yawkat/GridFlock/docs/images/edge-puzzle-clickgroove.png

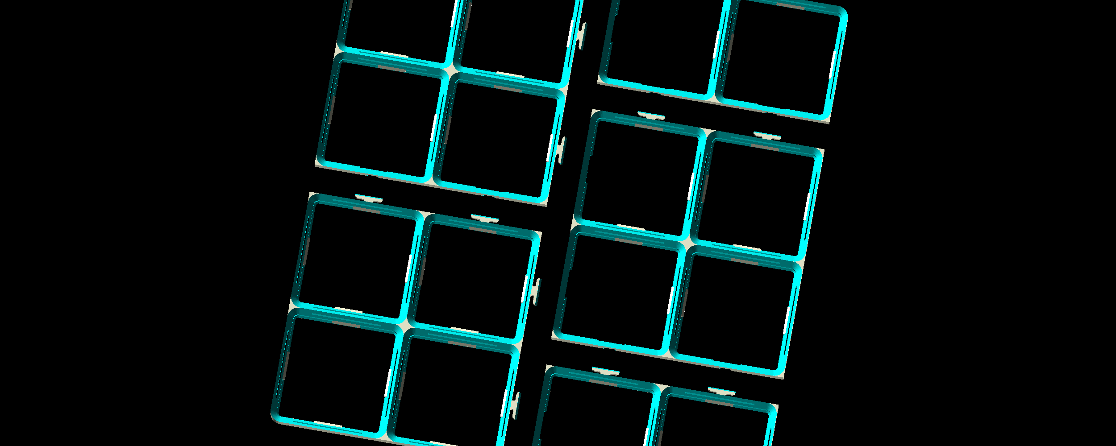
docs/images/edge-puzzle-clickgroove.png
