yawkat/GridFlock/docs/screenshot-generator-perplexinglabs.png

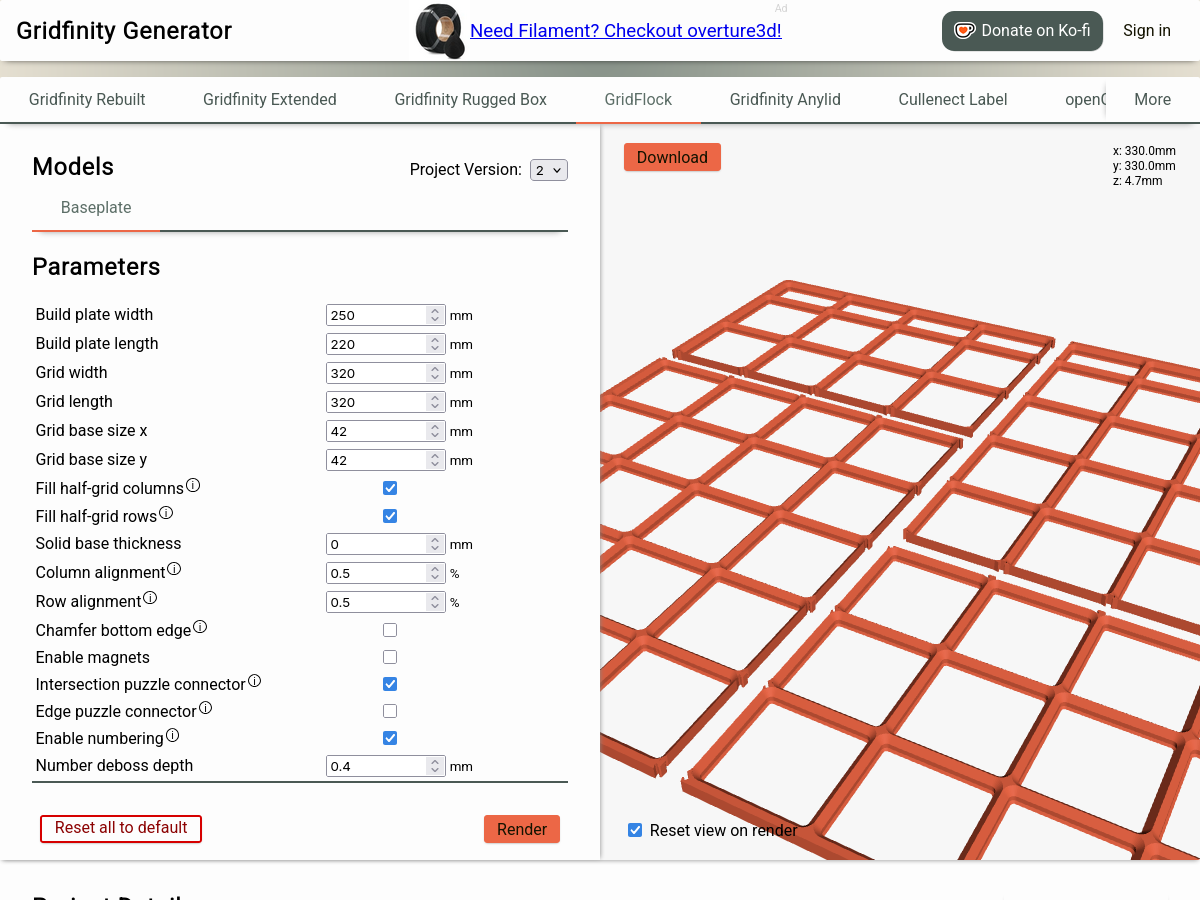
docs/screenshot-generator-perplexinglabs.png
