yawkat/GridFlock/docs/screenshot-generator-yawkat.png

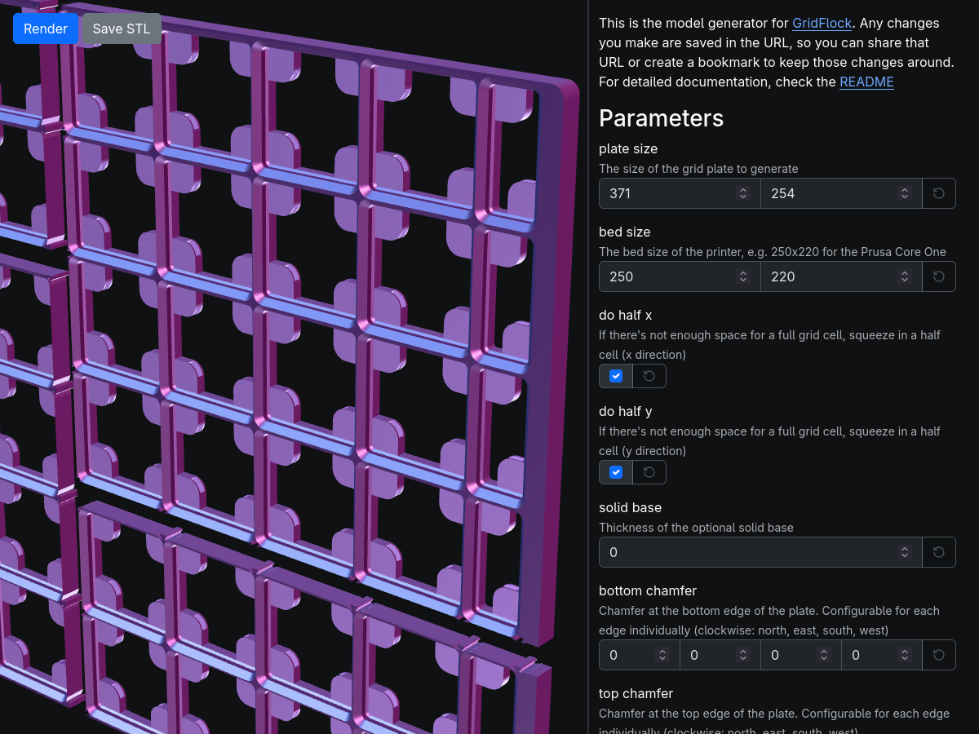
docs/screenshot-generator-yawkat.png
